creare-com/OpenTact/Docs/Images/Electronics/Tympan RevD3.jpg

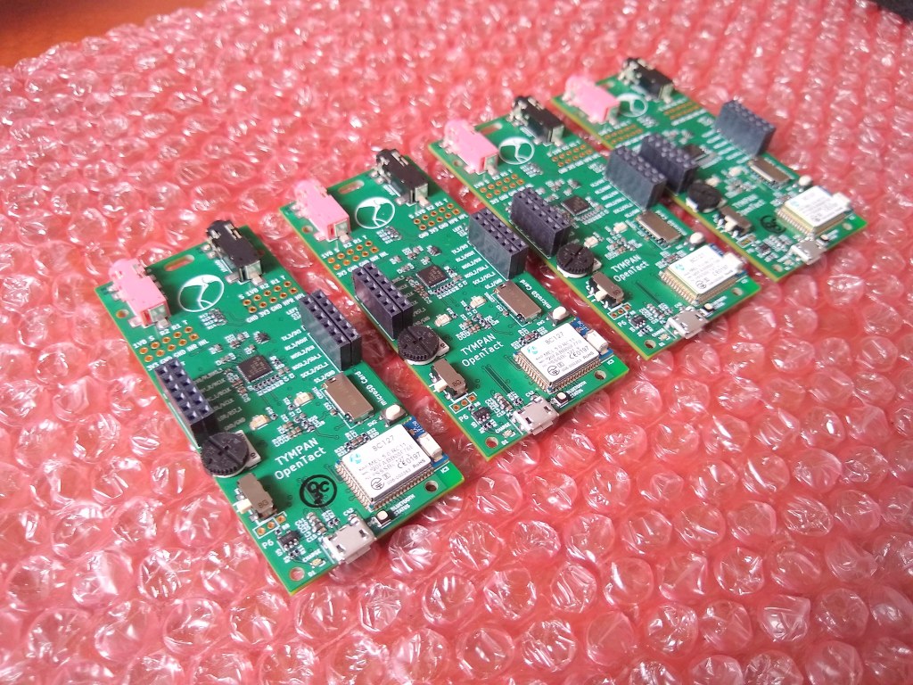
Docs/Images/Electronics/Tympan RevD3.jpg
