creare-com/OpenTact/Docs/Images/Electronics/Tympan_RevD3_inEnclosures.jpg

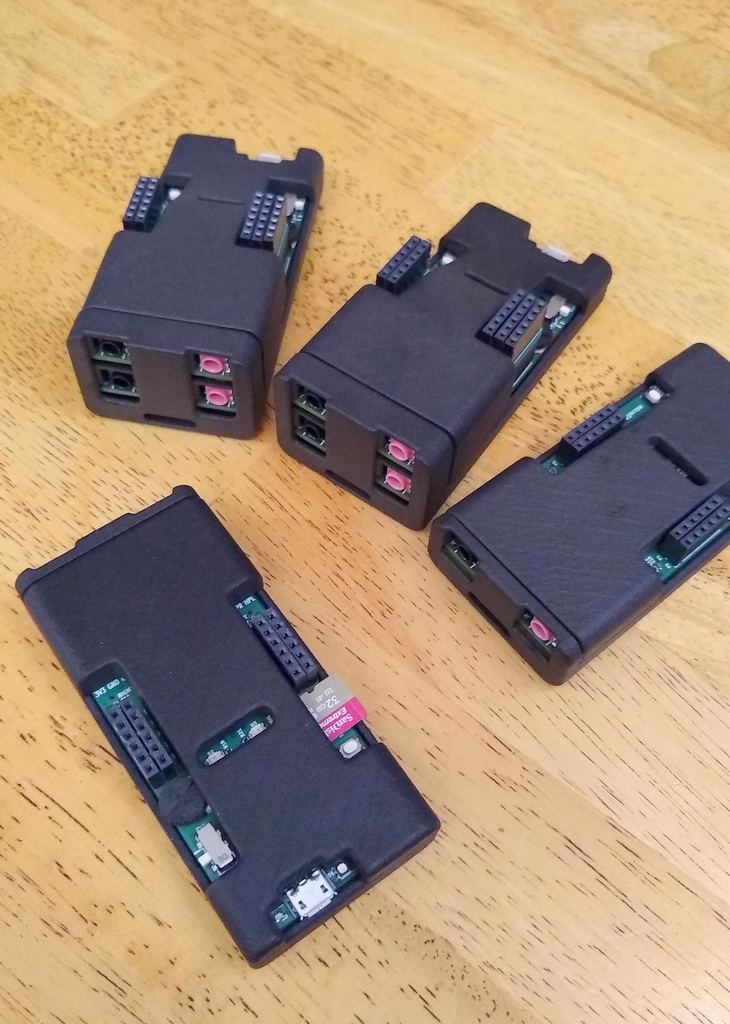
Docs/Images/Electronics/Tympan_RevD3_inEnclosures.jpg
