creare-com/OpenTact/Docs/Images/Headsets/Ears-onHead1-LeftSide.jpg

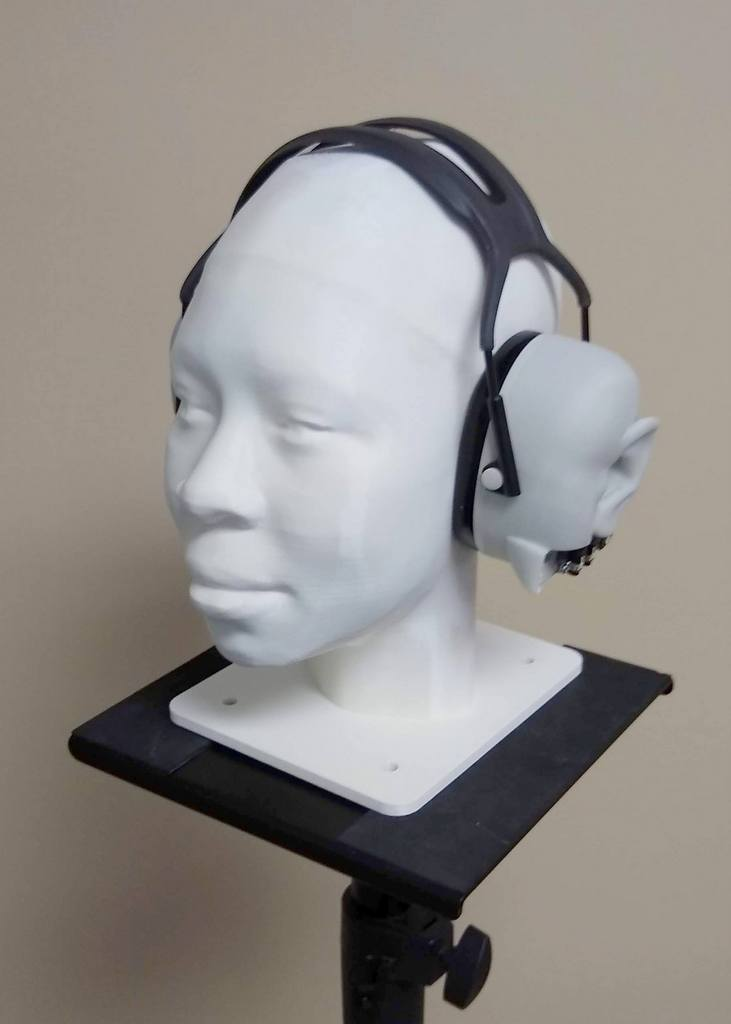
Docs/Images/Headsets/Ears-onHead1-LeftSide.jpg
