creare-com/OpenTact/Docs/Images/Headsets/Ears-onHead1-RightSide.jpg

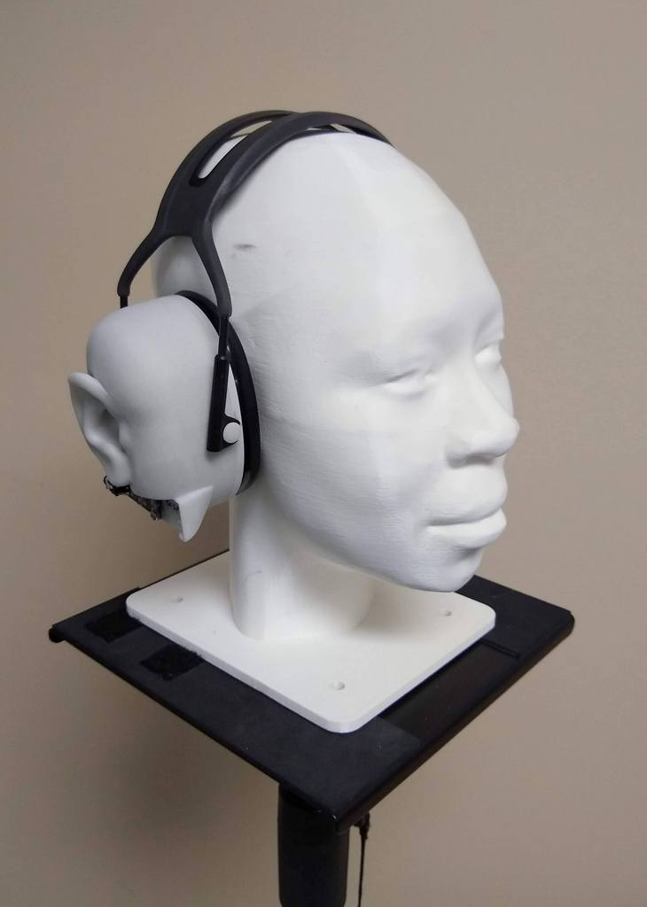
Docs/Images/Headsets/Ears-onHead1-RightSide.jpg
