creare-com/OpenTact/Docs/Images/Headsets/Ears-onHead2-HardLeft.jpg

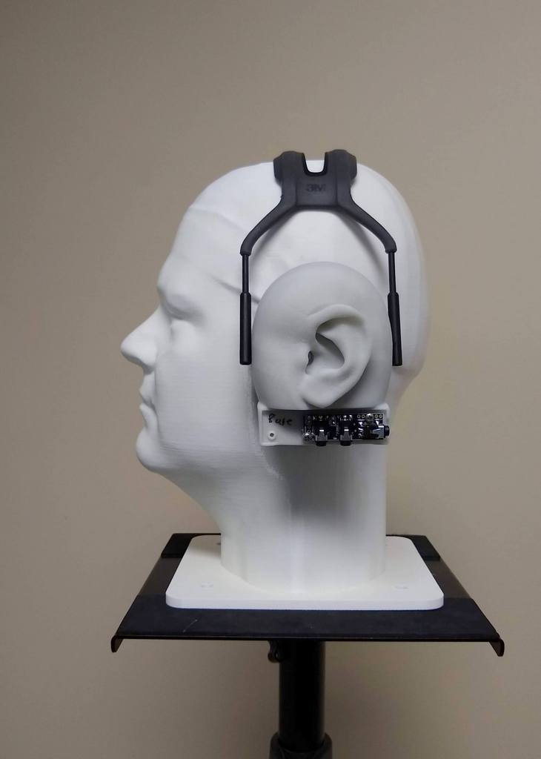
Docs/Images/Headsets/Ears-onHead2-HardLeft.jpg
