creare-com/OpenTact/Docs/Images/Headsets/Ears-onHead2-LeftSide.png

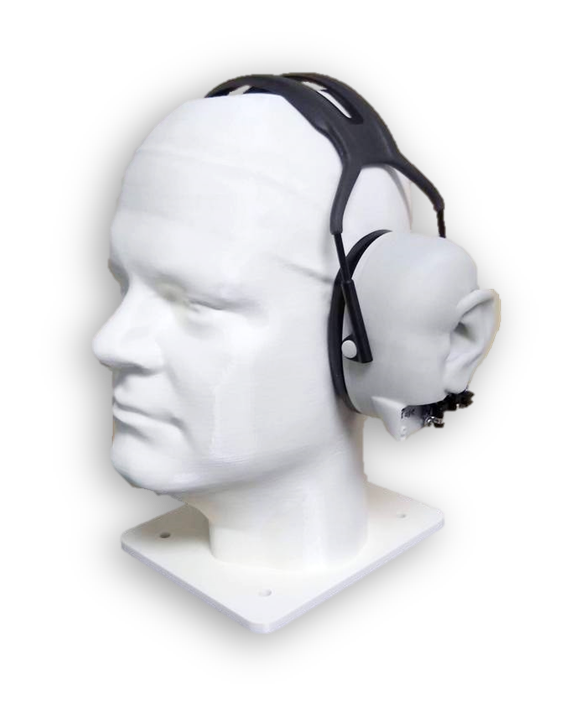
Docs/Images/Headsets/Ears-onHead2-LeftSide.png
