creare-com/OpenTact/Docs/Images/Headsets/EarsOff-onHead2-HardLeft.jpg

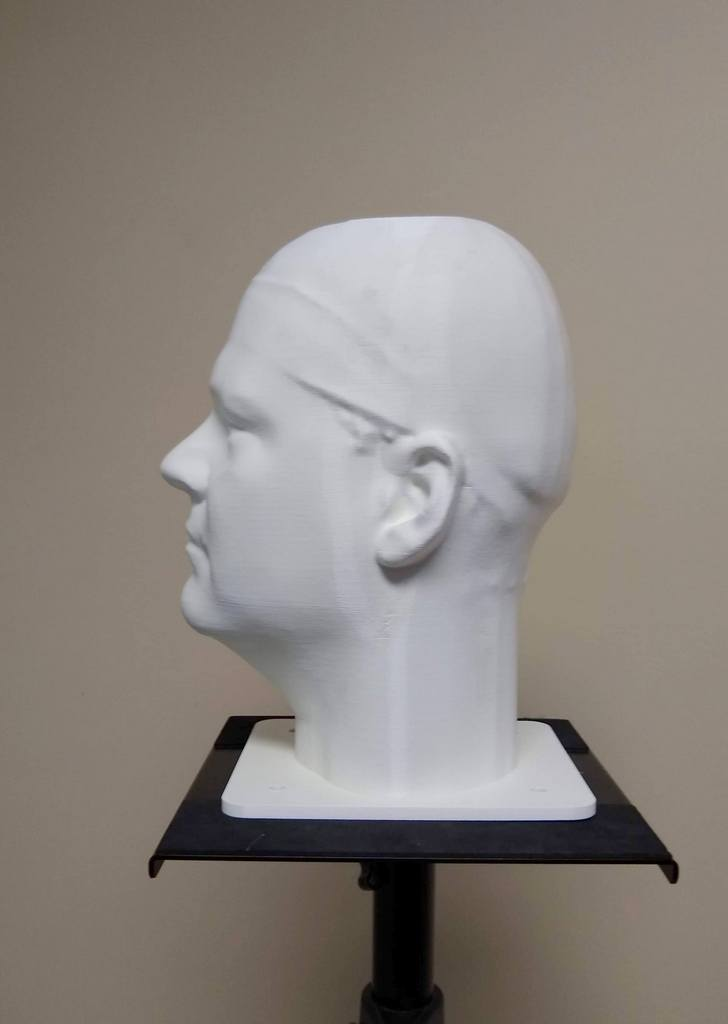
Docs/Images/Headsets/EarsOff-onHead2-HardLeft.jpg
