creare-com/OpenTact/Docs/Images/Headsets/FullPro-OnHead1-LeftSide.jpg

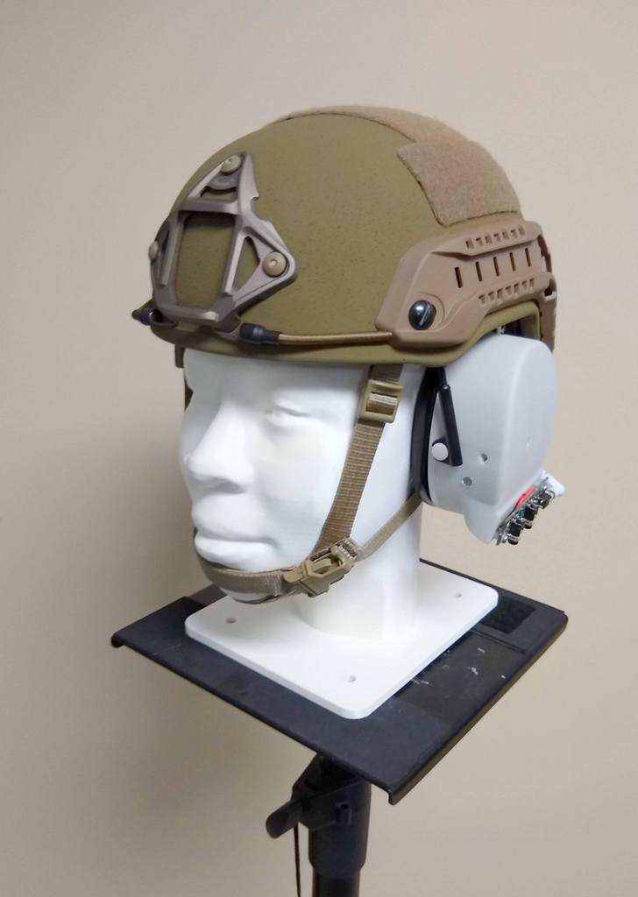
Docs/Images/Headsets/FullPro-OnHead1-LeftSide.jpg
