creare-com/OpenTact/Docs/Images/Headsets/FullPro-onHead1-RightSide.jpg

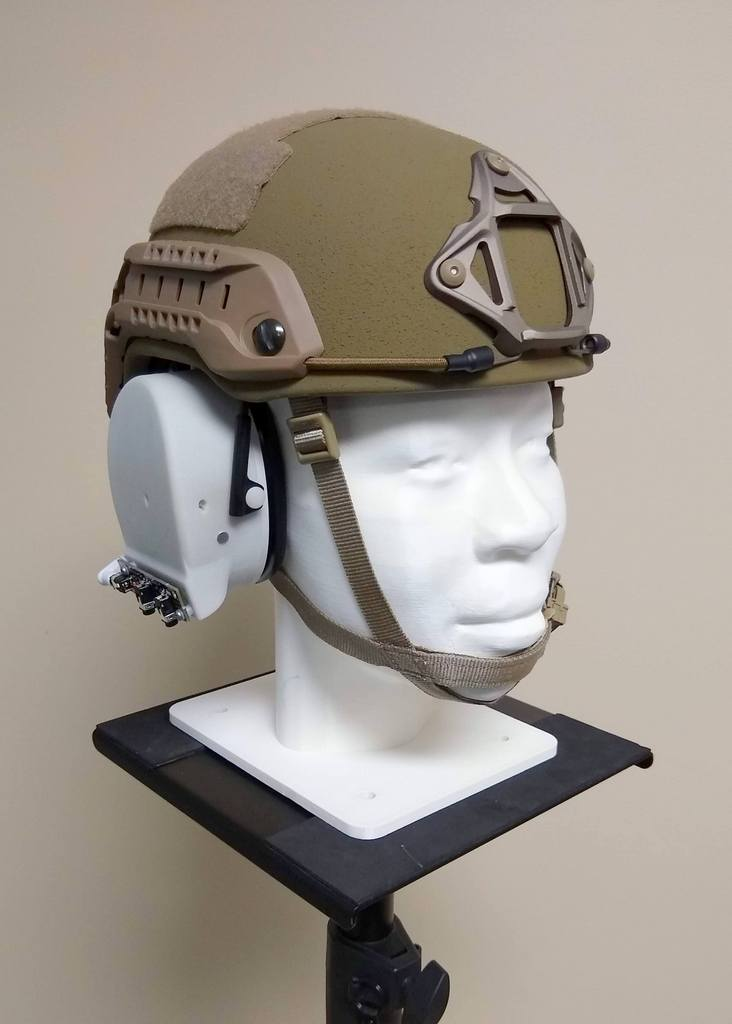
Docs/Images/Headsets/FullPro-onHead1-RightSide.jpg
