creare-com/OpenTact/Docs/Images/Headsets/FullPro-onHead2-LeftSide.png

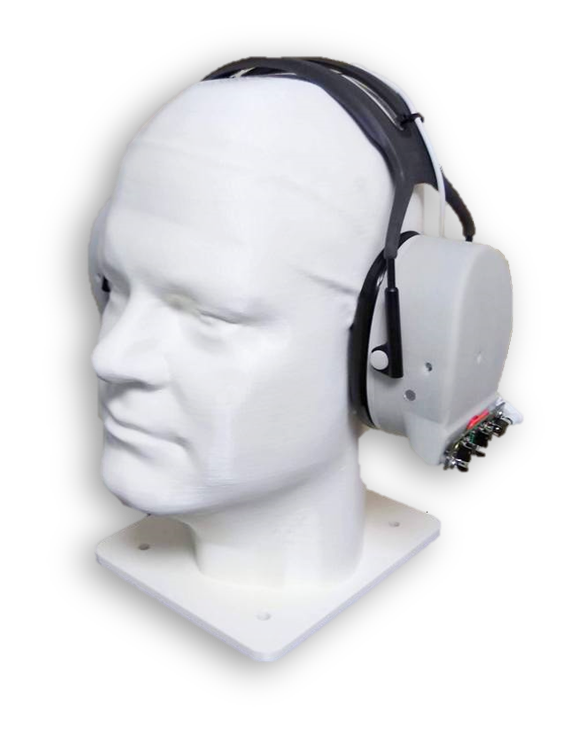
Docs/Images/Headsets/FullPro-onHead2-LeftSide.png
