creare-com/OpenTact/Docs/Images/Headsets/LoPro-onHead1-wHelmet-LeftSide.png

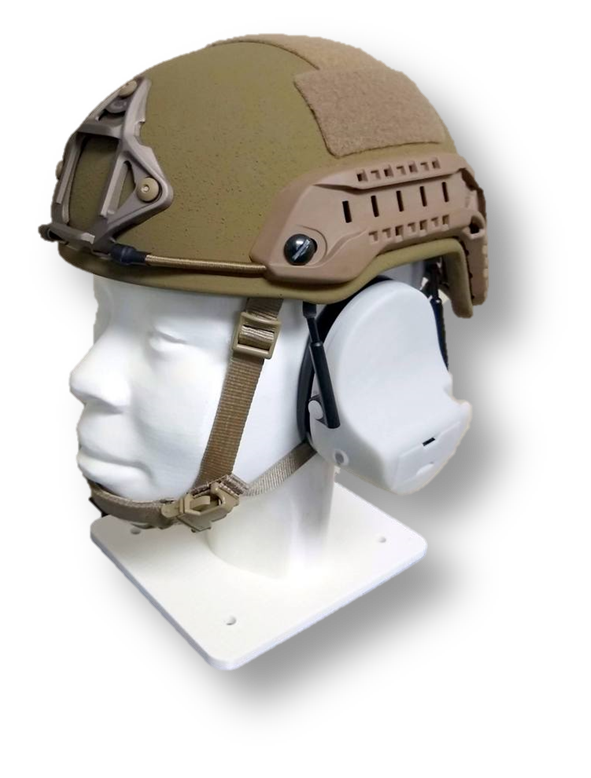
Docs/Images/Headsets/LoPro-onHead1-wHelmet-LeftSide.png
