creare-com/OpenTact/Docs/Images/Headsets/LoPro-onHead1-wHelmet-RightSide.png

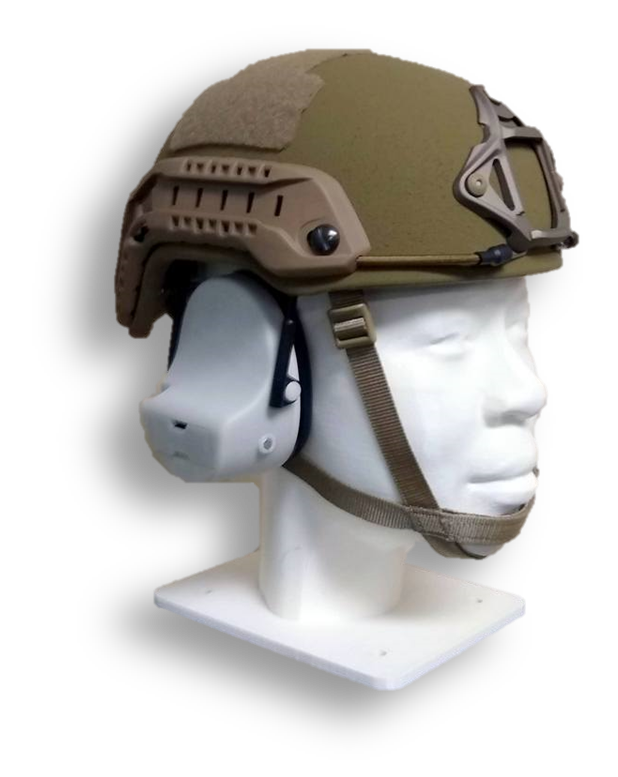
Docs/Images/Headsets/LoPro-onHead1-wHelmet-RightSide.png
