creare-com/OpenTact/Docs/Images/Headsets/LowPro-onHead1-LeftSide.png

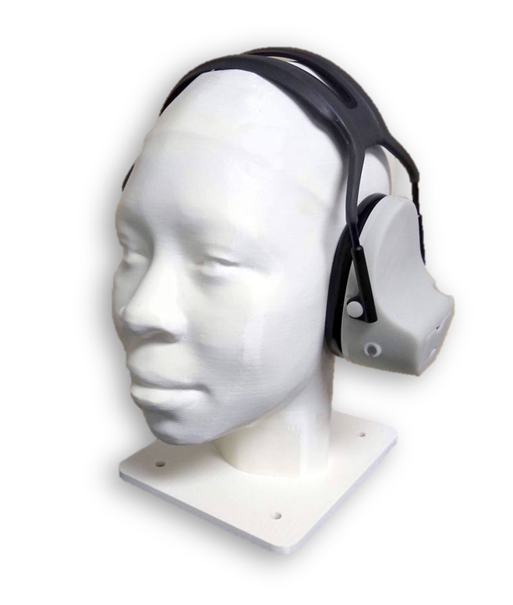
Docs/Images/Headsets/LowPro-onHead1-LeftSide.png
