creare-com/OpenTact/Docs/Images/Testing_GRAS45CB/ClearEars-GRAS45CB.jpg

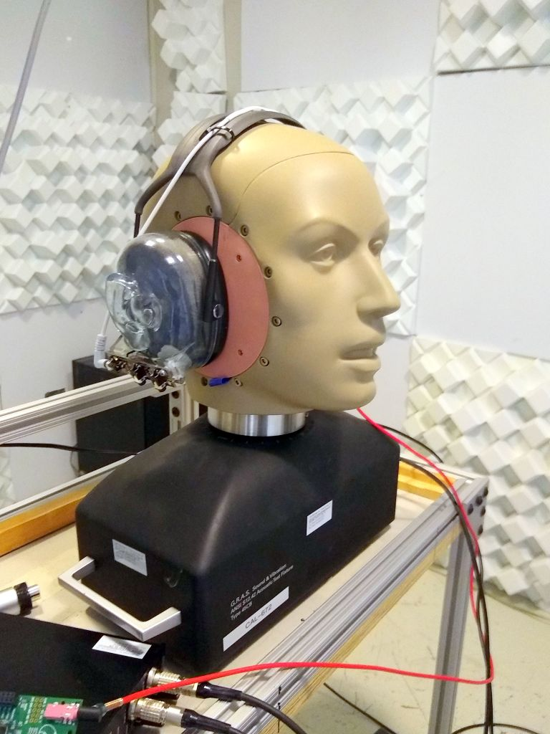
Docs/Images/Testing_GRAS45CB/ClearEars-GRAS45CB.jpg
