creare-com/OpenTact/Docs/Images/Testing_GRAS45CB/ClearEars-withTympan.jpg

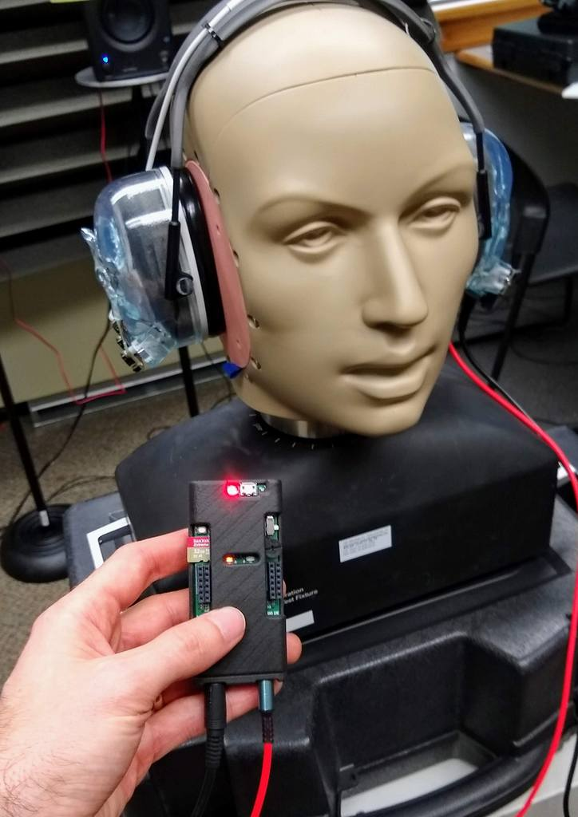
Docs/Images/Testing_GRAS45CB/ClearEars-withTympan.jpg
