creare-com/OpenTact/Docs/Images/Testing_GRAS45CB/ComTacIII-GRAS45CB.jpg

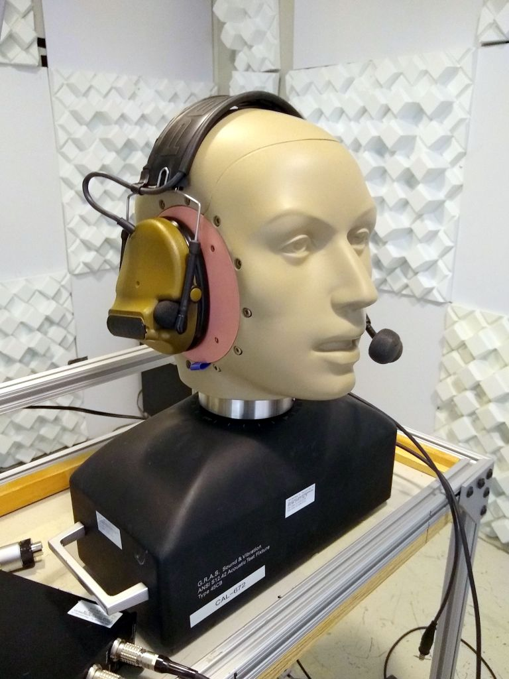
Docs/Images/Testing_GRAS45CB/ComTacIII-GRAS45CB.jpg
