creare-com/OpenTact/Docs/Images/Testing_GRAS45CB/FullPro-GRAS45CB.jpg

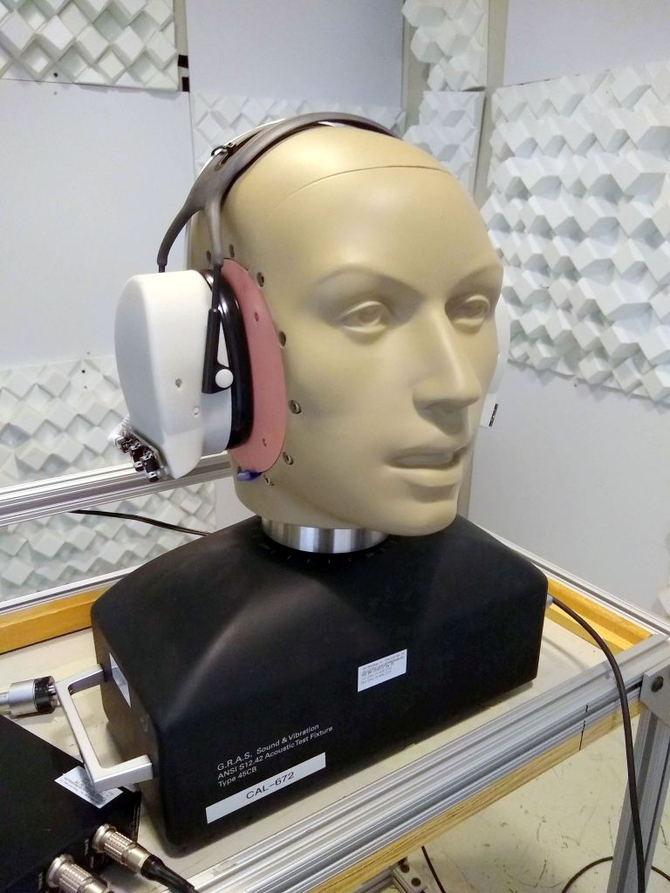
Docs/Images/Testing_GRAS45CB/FullPro-GRAS45CB.jpg
