creare-com/OpenTact/Docs/Images/Testing_GRAS45CB/LoPro-FromFront.jpg

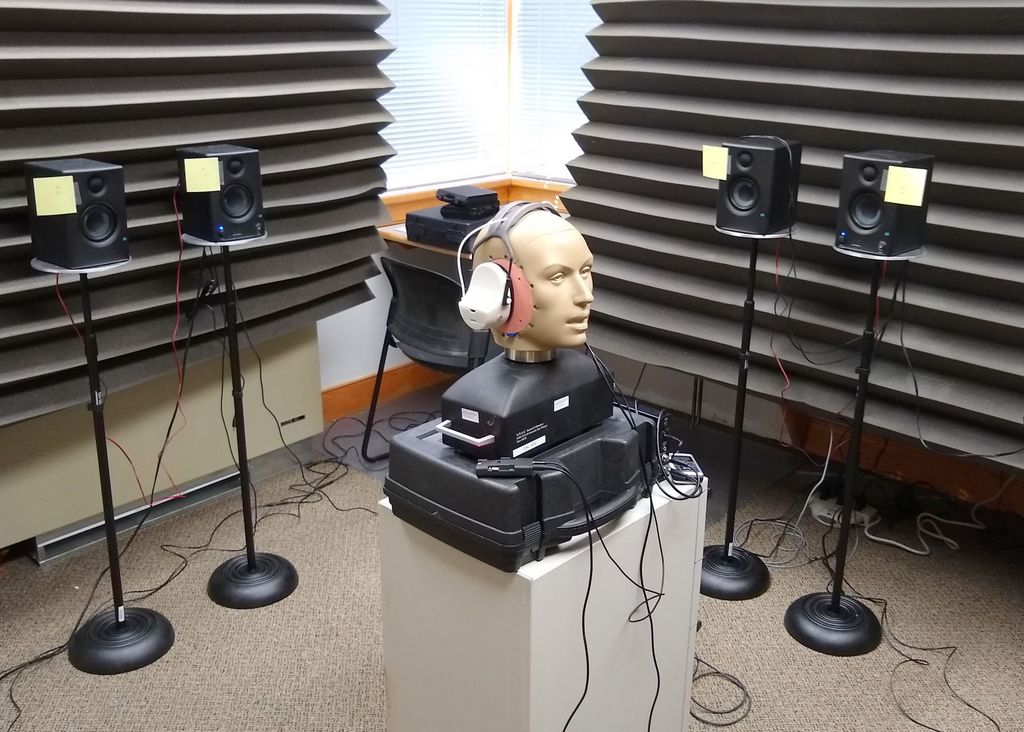
Docs/Images/Testing_GRAS45CB/LoPro-FromFront.jpg
