creare-com/OpenTact/Docs/Images/Testing_GRAS45CB/LoPro-FromRear.jpg

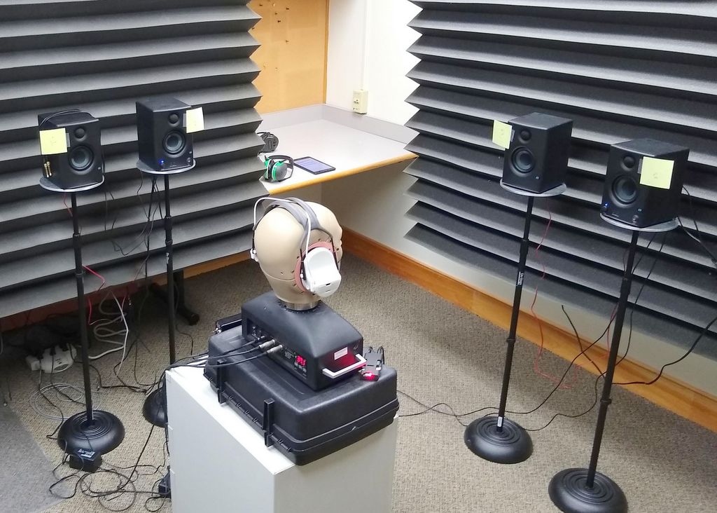
Docs/Images/Testing_GRAS45CB/LoPro-FromRear.jpg
