creare-com/OpenTact/Docs/Images/Testing_GRAS45CB/LoPro-Side.jpg

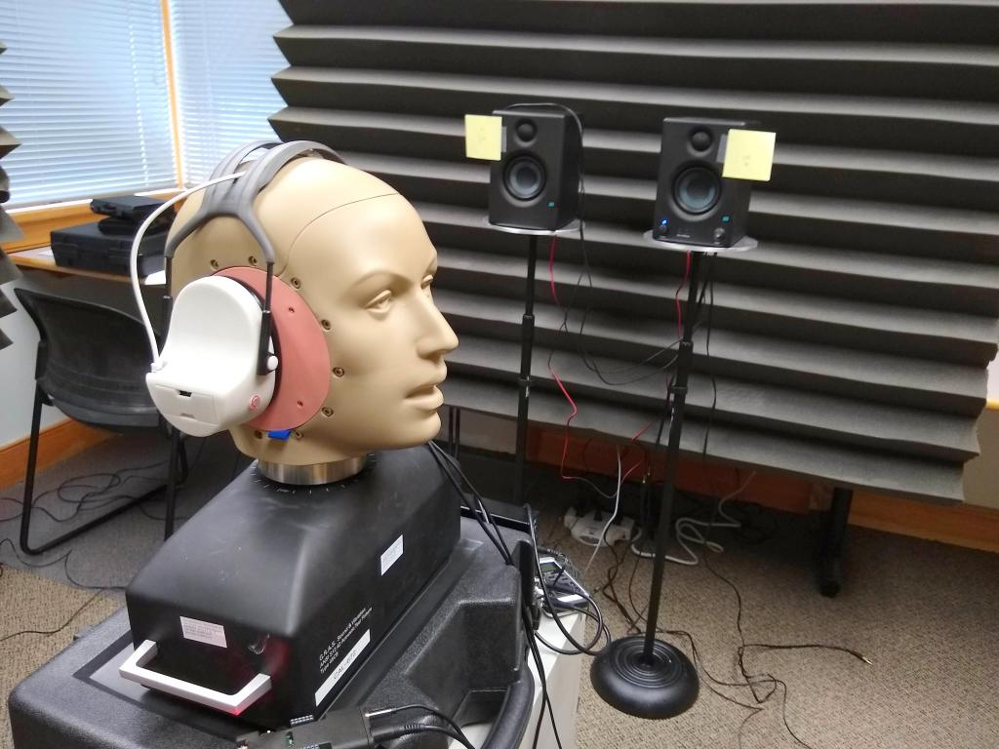
Docs/Images/Testing_GRAS45CB/LoPro-Side.jpg
