creare-com/OpenTact/Docs/Images/Testing_wPeople/Testing-Fend-LoPro-02.jpg

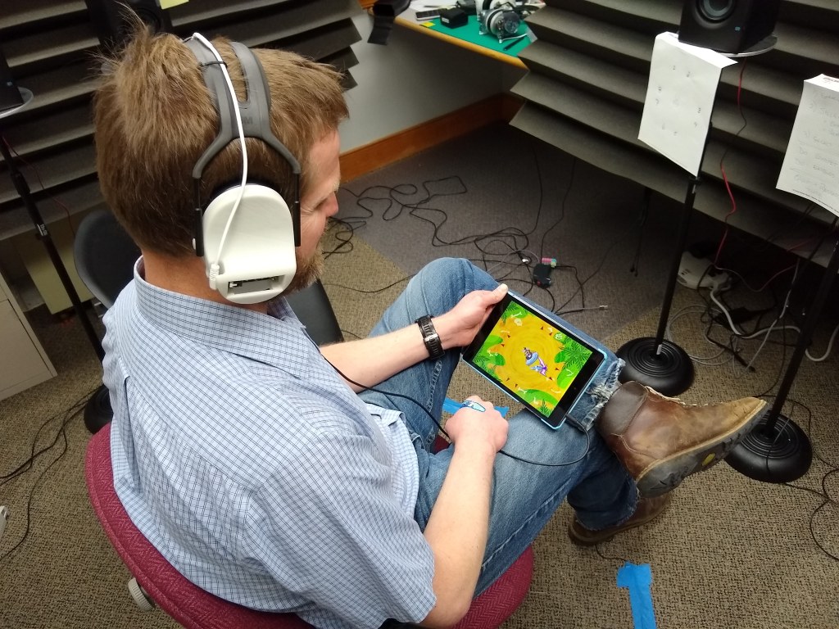
Docs/Images/Testing_wPeople/Testing-Fend-LoPro-02.jpg
