creare-com/OpenTact/Docs/Images/Testing_wPeople/Testing-Localization-ComTacIII-01.jpg

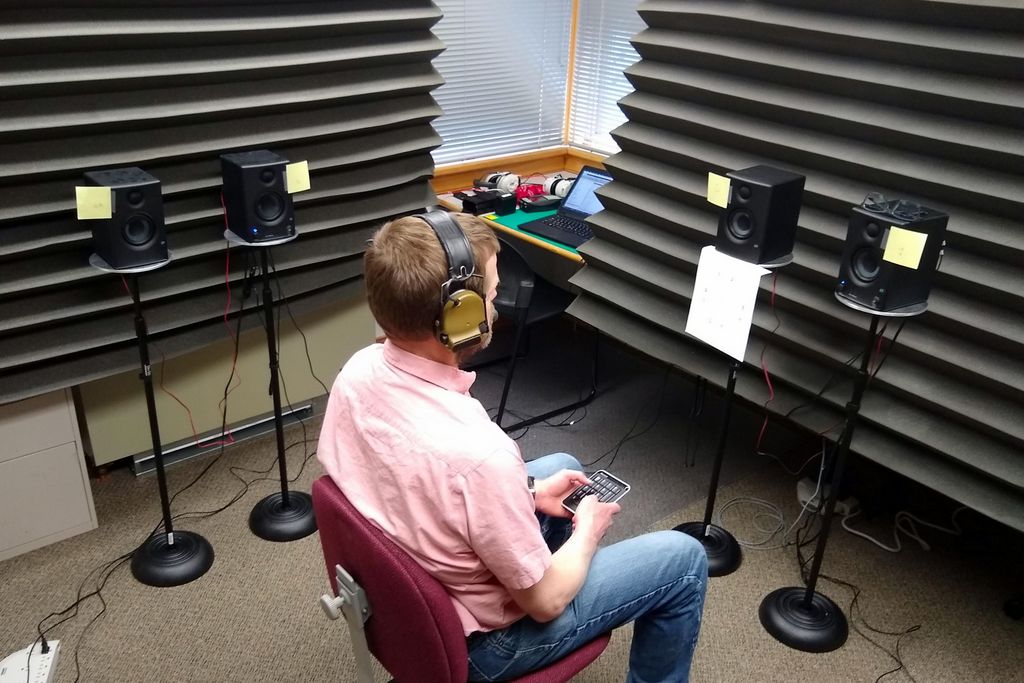
Docs/Images/Testing_wPeople/Testing-Localization-ComTacIII-01.jpg
