creare-com/OpenTact/Docs/Images/Testing_wPeople/Testing-Localization-LoPro-01.jpg

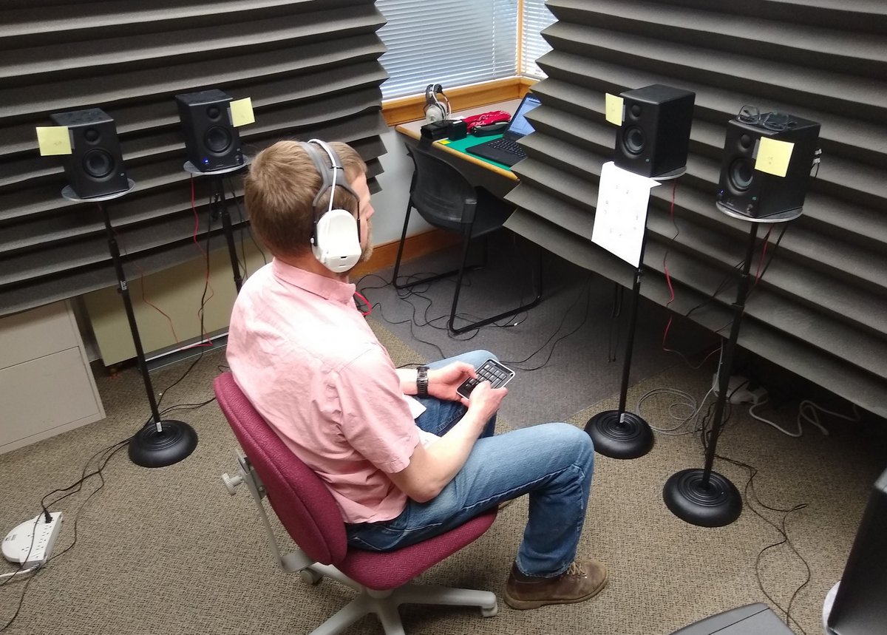
Docs/Images/Testing_wPeople/Testing-Localization-LoPro-01.jpg
